ThomasHFWright/apollo-3d-enclosure/output/compact-corner-poe/apollo-mount.FCStd

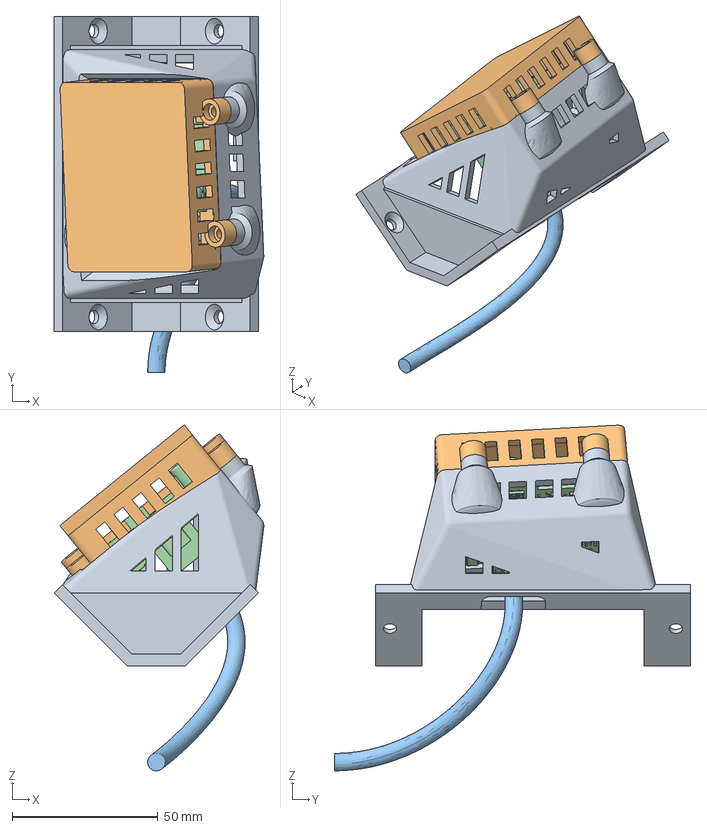
[picture p25: CAD file, 2026-09-16]
output/compact-corner-poe/apollo-mount.FCStd
71.8 x 122.0 x 118.5 mm
Structural mount - one printed part
Front cover and PCB keepers
Cable route preview - reference only, NOT printed
Original PCB mesh - radar and CO2 boards absent
