ThomasHFWright/apollo-3d-enclosure/output/corner/body.step

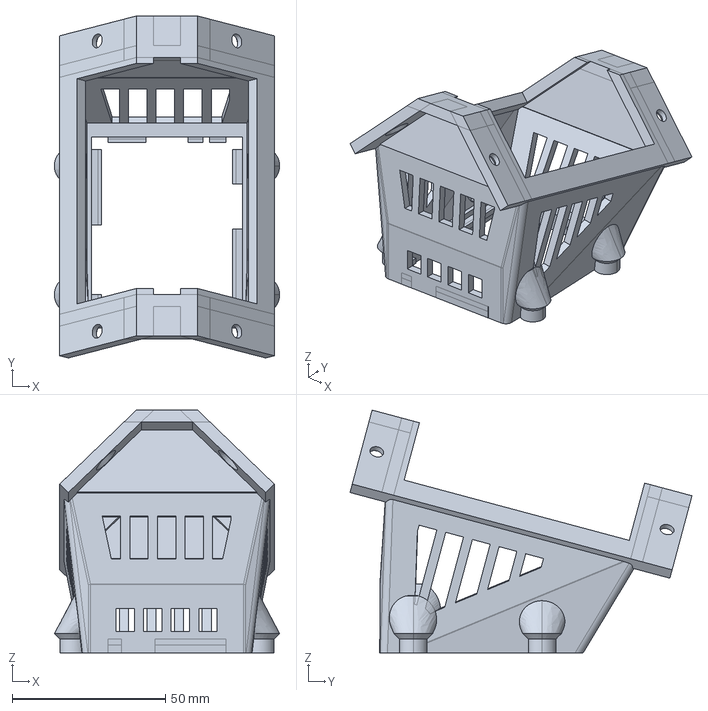
[picture p26: CAD file, 2026-09-16]
output/corner/body.step
73.5 x 111.5 x 79.2 mm
