ThomasHFWright/apollo-3d-enclosure/output/custom/body.step

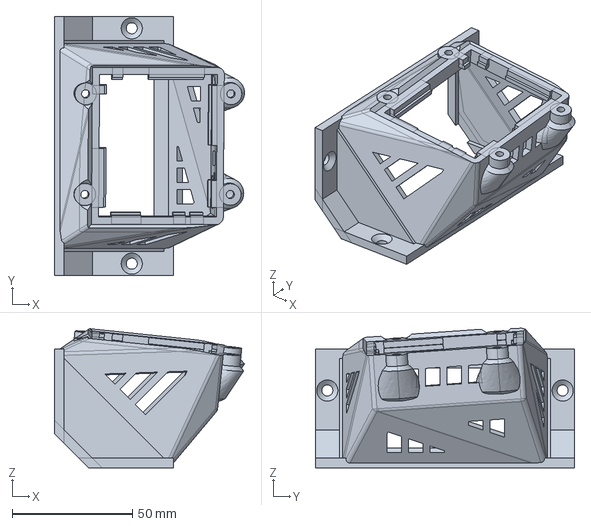
[picture p27: CAD file, 2026-09-16]
output/custom/body.step
79.1 x 108.0 x 58.1 mm
