ThomasHFWright/apollo-3d-enclosure/output/yaw90/apollo-mount.FCStd

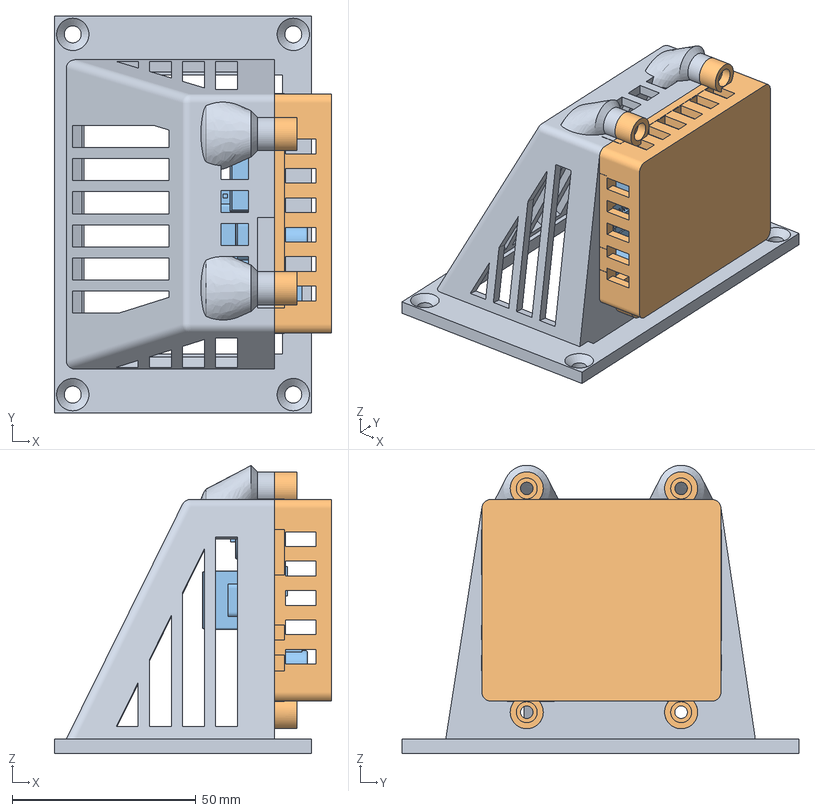
[picture p28: CAD file, 2026-09-16]
output/yaw90/apollo-mount.FCStd
75.4 x 108.0 x 78.5 mm
Structural mount - one printed part
Front cover and PCB keepers
Original PCB mesh - radar and CO2 boards absent
