ThomasHFWright/apollo-3d-enclosure/output/compact-corner-poe/body.step

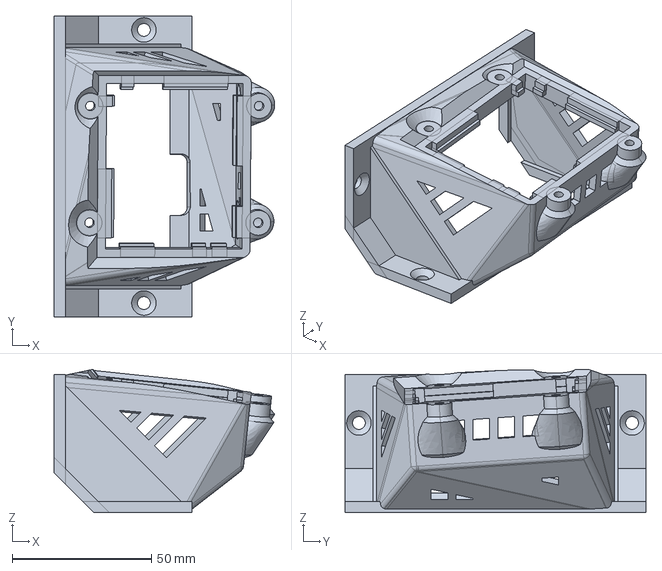
[picture p29: CAD file, 2026-09-16]
output/compact-corner-poe/body.step
79.1 x 108.0 x 51.4 mm
