ThomasHFWright/apollo-3d-enclosure/output/compact-pitch15/body.step

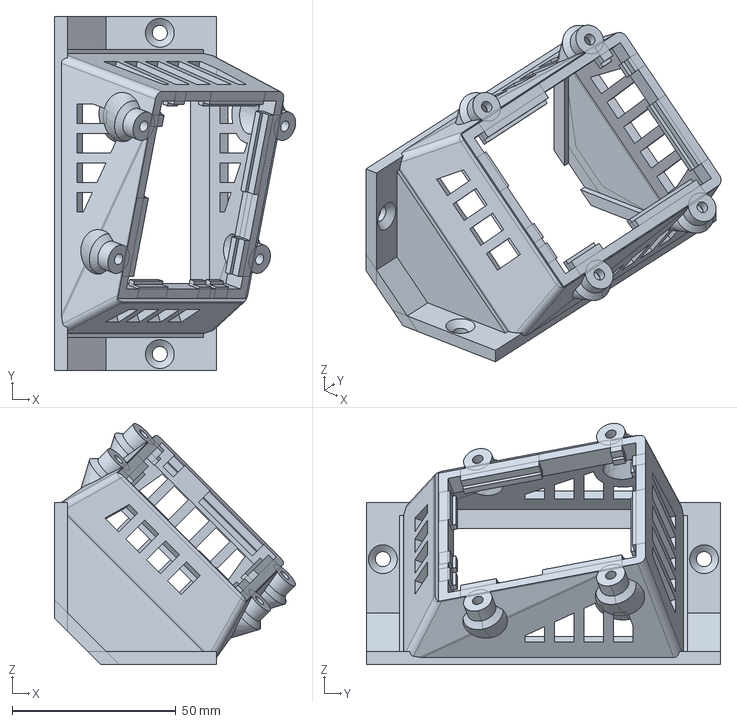
[picture p30: CAD file, 2026-09-16]
output/compact-pitch15/body.step
73.6 x 108.0 x 73.6 mm
