ThomasHFWright/apollo-3d-enclosure/output/corner/apollo-mount.FCStd

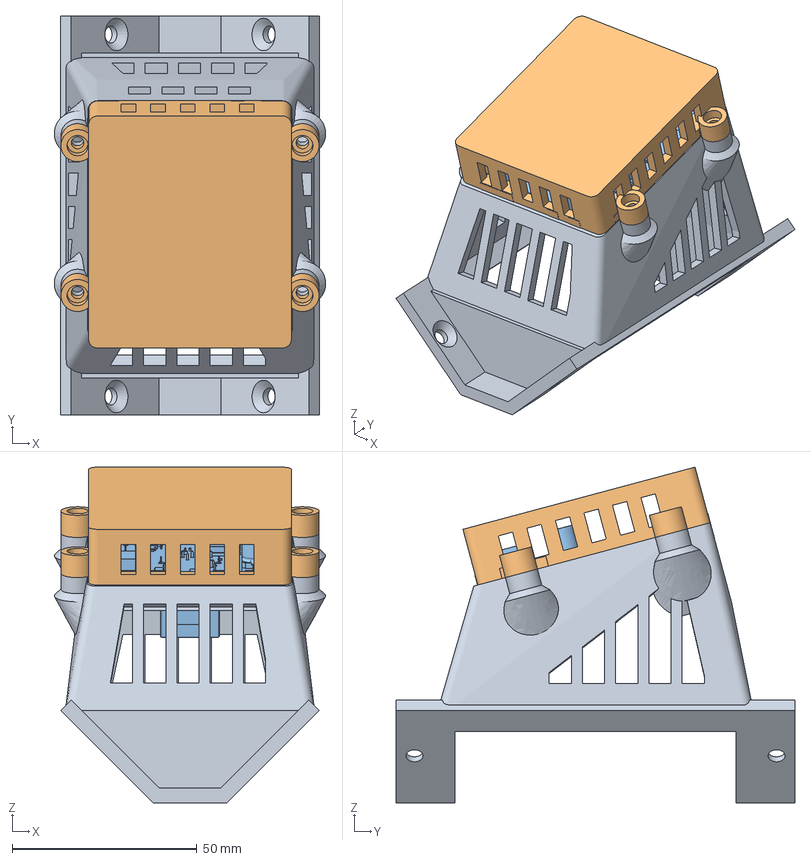
[picture p31: CAD file, 2026-09-16]
output/corner/apollo-mount.FCStd
73.5 x 108.0 x 90.9 mm
Structural mount - one printed part
Front cover and PCB keepers
Original PCB mesh - radar and CO2 boards absent
