ThomasHFWright/apollo-3d-enclosure/output/flat/apollo-mount.FCStd

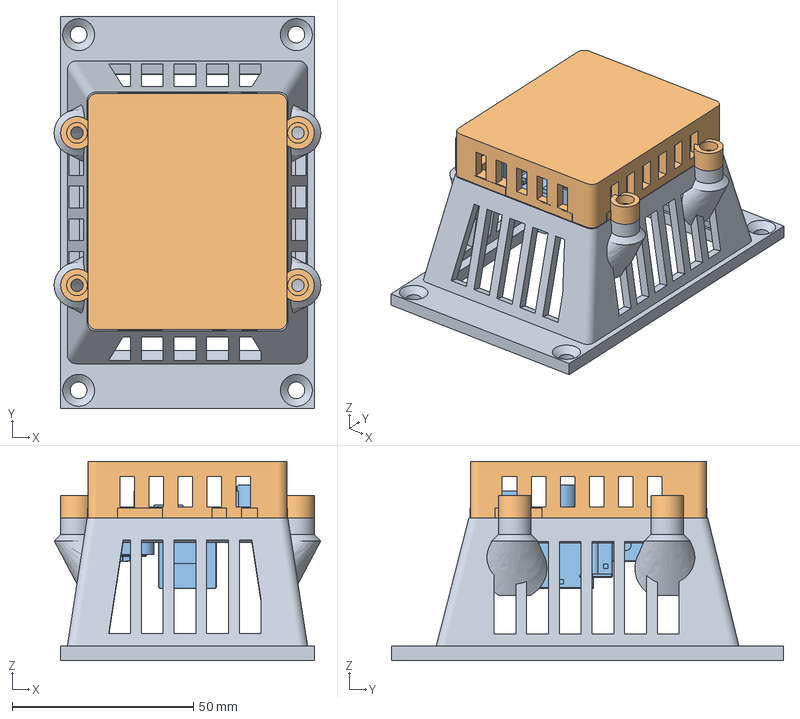
[picture p32: CAD file, 2026-09-16]
output/flat/apollo-mount.FCStd
73.5 x 108.0 x 54.9 mm
Structural mount - one printed part
Front cover and PCB keepers
Original PCB mesh - radar and CO2 boards absent
